MrTG1B/Handy-Hacksprint/Block Diagram/block diagram.png

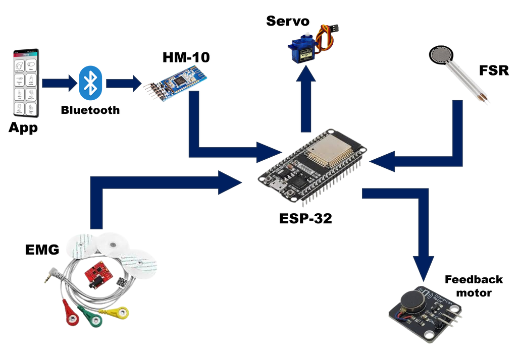
Block Diagram/block diagram.png
