MrTG1B/Handy-Hacksprint/Design/STL-FILES/MIDDLE-2.stl

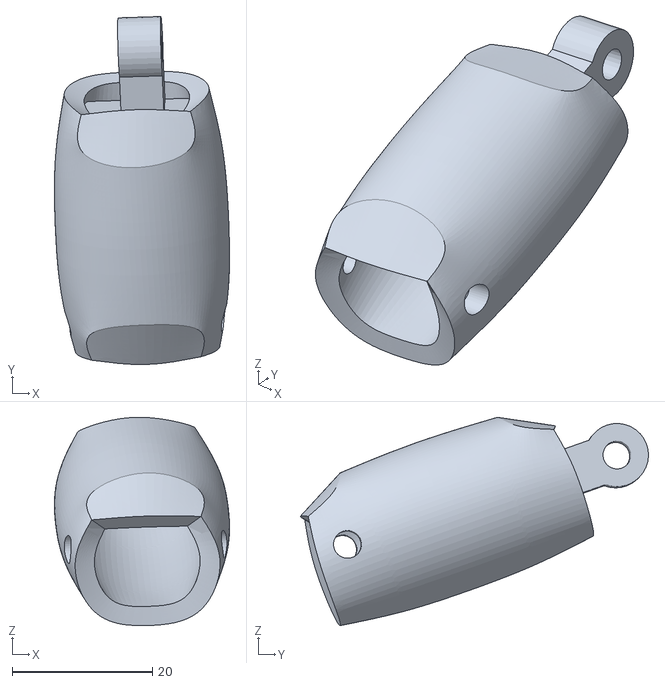
[picture p30: CAD file, 2025-11-02]
Design/STL-FILES/MIDDLE-2.stl
25.0 x 49.7 x 29.7
