MrTG1B/Handy-Hacksprint/Design/STL-FILES/Grind.stl

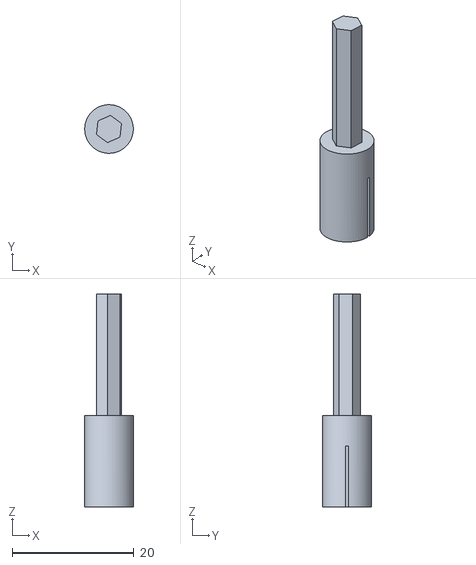
[picture p31: CAD file, 2025-11-02]
Design/STL-FILES/Grind.stl
8.00 x 8.00 x 35.0
