MrTG1B/Handy-Hacksprint/Design/STL-FILES/INDEX-2.stl

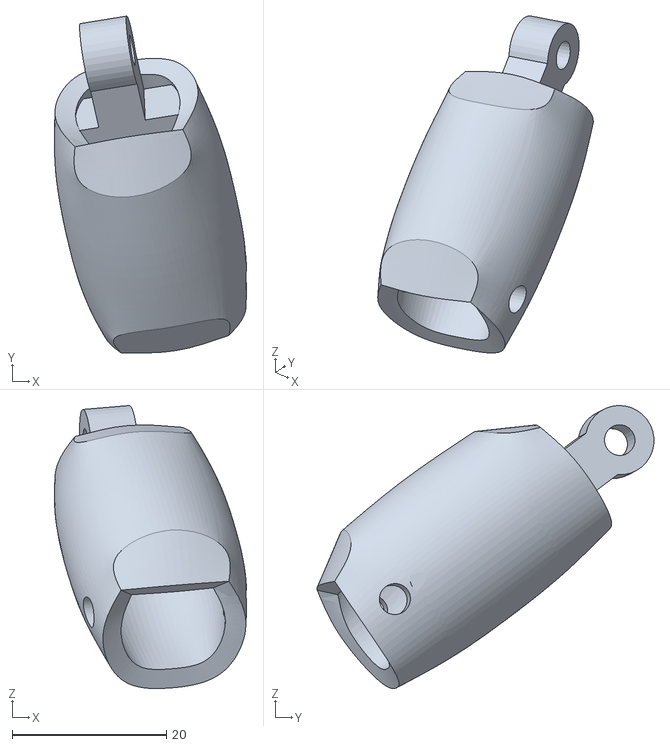
[picture p32: CAD file, 2025-11-02]
Design/STL-FILES/INDEX-2.stl
24.9 x 43.6 x 36.6
