MrTG1B/Handy-Hacksprint/Design/STL-FILES/RING-3.stl

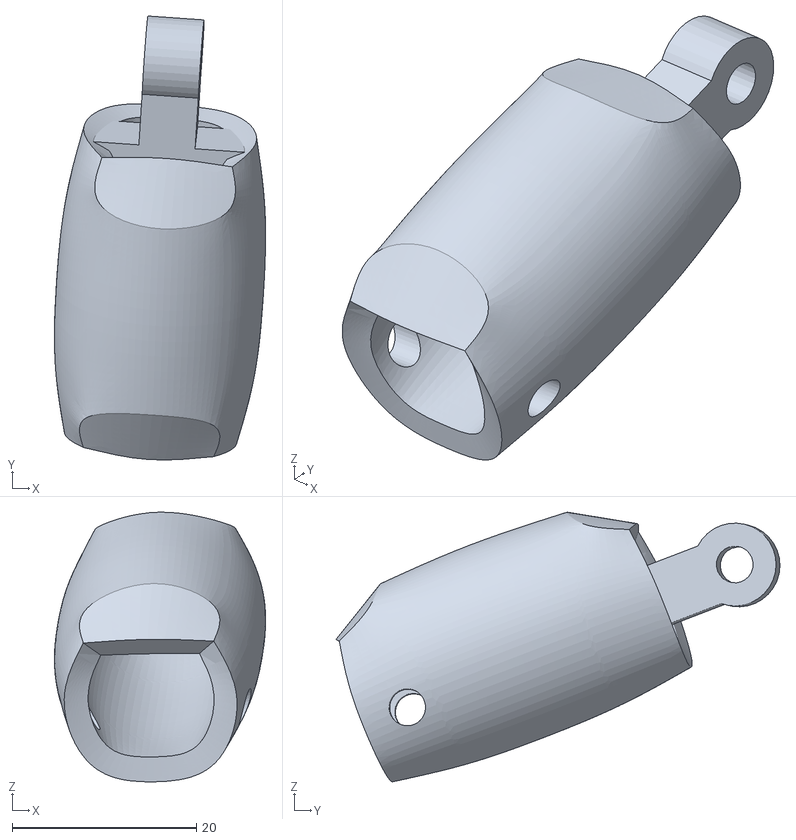
[picture p33: CAD file, 2025-11-02]
Design/STL-FILES/RING-3.stl
23.0 x 48.3 x 29.3
