MrTG1B/Handy-Hacksprint/Design/STL-FILES/BACK PLATE.stl

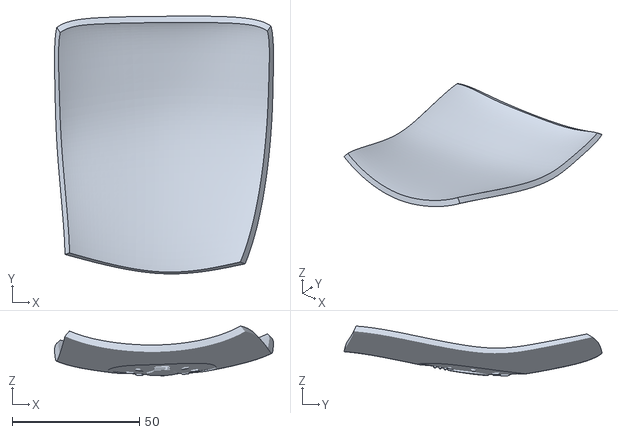
[picture p34: CAD file, 2025-11-02]
Design/STL-FILES/BACK PLATE.stl
86.0 x 101.3 x 19.6
