MrTG1B/Handy-Hacksprint/Design/STL-FILES/PALM.stl

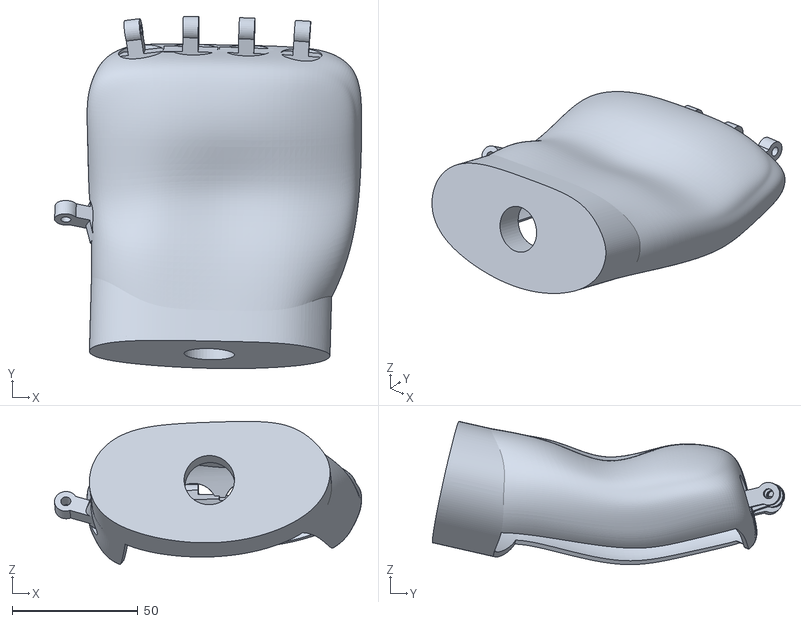
[picture p35: CAD file, 2025-11-02]
Design/STL-FILES/PALM.stl
121.9 x 139.8 x 56.9
